MichMich/DigitalTrainController/src/RandomTimeTask.cpp

#include "RandomTimeTask.h"

    RandomTimeTask::RandomTimeTask(uint32_t time) : Task(MsToTaskTime(MsToTaskTime(time)))
    { 
        _minimumTime = MsToTaskTime(time);
        _maximumTime = MsToTaskTime(time);
    };

    unsigned long RandomTimeTask::remainingTime() 
    {
        return _remainingTime;
    }
    unsigned long RandomTimeTask::remainingTimeInSeconds() 
    {
        return 1 + ((_remainingTime - 1) / 1000); ;
    }

    void RandomTimeTask::setCallback(TaskCallbackFunction callback) {
        _callback = callback;
    }

    void RandomTimeTask::setMinMaxTime(uint32_t minimumTime, uint32_t maximumTime) {
        _minimumTime = MsToTaskTime(minimumTime);
        _maximumTime = MsToTaskTime(maximumTime);
        setTimeInterval(random(_minimumTime, _maximumTime));
    }

    bool RandomTimeTask::OnStart() // optional
    {
        setTimeInterval(random(_minimumTime, _maximumTime));
        return true;
    }

    void RandomTimeTask::OnUpdate(uint32_t deltaTime)
    {
        _callback();
        setTimeInterval(random(_minimumTime, _maximumTime));
    }
